Squalius-cephalus/silakka18/firmware/silakka18/keymaps/vial/config.h

/* SPDX-License-Identifier: GPL-2.0-or-later */

#pragma once


#define VIAL_KEYBOARD_UID {0xC7, 0x8F, 0x7C, 0x31, 0x3E, 0xFB, 0x37, 0x3E}

#define VIAL_UNLOCK_COMBO_ROWS { 0, 1 }
#define VIAL_UNLOCK_COMBO_COLS { 1, 1 }
